Randomwaves/Synthgirl/02 Software/Synthgirl-App-H723/Data/Design 480x854/Image_Osc_B.bmp

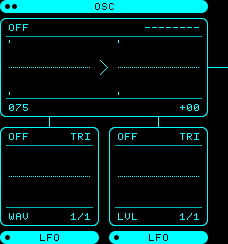
02 Software/Synthgirl-App-H723/Data/Design 480x854/Image_Osc_B.bmp
