Randomwaves/Synthgirl/02 Software/Synthgirl-App-H723/Data/Lfo/Lfo.pde

//int[] tri1  = {0, 128, 256, 384, 512, 640, 768, 896, 1024, 1152, 1280, 1408, 1536, 1664, 1792, 1920, 2048, 2176, 2304, 2432, 2560, 2688, 2816, 2944, 3072, 3200, 3328, 3456, 3584, 3712, 3840, 3968, 4096, 4224, 4352, 4480, 4608, 4736, 4864, 4992, 5120, 5248, 5376, 5504, 5632, 5760, 5888, 6016, 6144, 6272, 6400, 6528, 6656, 6784, 6912, 7040, 7168, 7296, 7424, 7552, 7680, 7808, 7936, 8064, 8192, 8320, 8448, 8576, 8704, 8832, 8960, 9088, 9216, 9344, 9472, 9600, 9728, 9856, 9984, 10112, 10240, 10368, 10496, 10624, 10752, 10880, 11008, 11136, 11264, 11392, 11520, 11648, 11776, 11904, 12032, 12160, 12288, 12416, 12544, 12672, 12800, 12928, 13056, 13184, 13312, 13440, 13568, 13696, 13824, 13952, 14080, 14208, 14336, 14464, 14592, 14720, 14848, 14976, 15104, 15232, 15360, 15488, 15616, 15744, 15872, 16000, 16128, 16256, 16384, 16512, 16640, 16768, 16896, 17024, 17152, 17280, 17408, 17536, 17664, 17792, 17920, 18048, 18176, 18304, 18432, 18560, 18688, 18816, 18944, 19072, 19200, 19328, 19456, 19584, 19712, 19840, 19968, 20096, 20224, 20352, 20480, 20608, 20736, 20864, 20992, 21120, 21248, 21376, 21504, 21632, 21760, 21888, 22016, 22144, 22272, 22400, 22528, 22656, 22784, 22912, 23040, 23168, 23296, 23424, 23552, 23680, 23808, 23936, 24064, 24192, 24320, 24448, 24576, 24704, 24832, 24960, 25088, 25216, 25344, 25472, 25600, 25728, 25856, 25984, 26112, 26240, 26368, 26496, 26624, 26752, 26880, 27008, 27136, 27264, 27392, 27520, 27648, 27776, 27904, 28032, 28160, 28288, 28416, 28544, 2867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
4, 46897, 47090, 47283, 47476, 47669, 47863, 48057, 48251, 48445, 48639, 48833, 49028, 49222, 49417, 49612, 49807, 50002, 50198, 50393, 50589, 50785, 50981, 51177, 51373, 51570, 51766, 51963, 52160, 52356, 52553, 52751, 52948, 53145, 53343, 53540, 53738, 53936, 54134, 54332, 54530, 54728, 54927, 55125, 55324, 55522, 55721, 55920, 56119, 56318, 56517, 56716, 56915, 57115, 57314, 57514, 57713, 57913, 58113, 58312, 58512, 58712, 58912, 59112, 59312, 59513, 59713, 59913, 60114, 60314, 60514, 60715, 60915, 61116, 61317, 61517, 61718, 61919, 62119, 62320, 62521, 62722, 62923, 63124, 63325, 63526, 63727, 63928, 64129, 64330, 64531, 64732, 64933, 65134, 65335, };

//int[] sine1 = {32768, 32969, 33170, 33371, 33572, 33773, 33974, 34175, 34376, 34577, 34777, 34978, 35179, 35379, 35579, 35780, 35980, 36180, 36380, 36580, 36779, 36979, 37178, 37377, 37576, 37775, 37973, 38172, 38370, 38568, 38766, 38963, 39161, 39358, 39555, 39751, 39948, 40144, 40339, 40535, 40730, 40925, 41119, 41314, 41508, 41701, 41895, 42087, 42280, 42472, 42664, 42856, 43047, 43237, 43428, 43618, 43807, 43996, 44185, 44373, 44561, 44748, 44935, 45122, 45308, 45493, 45678, 45863, 46047, 46231, 46414, 46596, 46778, 46960, 47141, 47321, 47501, 47680, 47859, 48037, 48215, 48392, 48568, 48744, 48919, 49094, 49268, 49441, 49614, 49786, 49958, 50129, 50299, 50468, 50637, 50805, 50973, 51140, 51306, 51471, 51636, 51800, 51963, 52126, 52288, 52449, 52609, 52769, 52928, 53086, 53243, 53400, 53556, 53711, 53865, 54019, 54171, 54323, 54474, 54624, 54774, 54922, 55070, 55217, 55363, 55508, 55652, 55796, 55938, 56080, 56221, 56361, 56500, 56638, 56776, 56912, 57047, 57182, 57316, 57448, 57580, 57711, 57841, 57970, 58098, 58225, 58351, 58476, 58601, 58724, 58846, 58967, 59088, 59207, 59325, 59442, 59559, 59674, 59788, 59901, 60014, 60125, 60235, 60344, 60452, 60559, 60665, 60770, 60874, 60977, 61079, 61179, 61279, 61378, 61475, 61571, 61667, 61761, 61854, 61946, 62037, 62127, 62216, 62303, 62390, 62475, 62560, 62643, 62725, 62806, 62886, 62964, 63042, 63118, 63193, 63267, 63340, 63412, 63483, 63552, 63621, 63688, 63754, 63818, 63882, 63945, 64006, 64066, 64125, 64183, 64239, 64295,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
1365, 11517, 11671, 11825, 11980, 12136, 12293, 12450, 12608, 12767, 12927, 13087, 13248, 13410, 13573, 13736, 13900, 14065, 14230, 14396, 14563, 14731, 14899, 15068, 15237, 15407, 15578, 15750, 15922, 16095, 16268, 16442, 16617, 16792, 16968, 17144, 17321, 17499, 17677, 17856, 18035, 18215, 18395, 18576, 18758, 18940, 19122, 19305, 19489, 19673, 19858, 20043, 20228, 20414, 20601, 20788, 20975, 21163, 21351, 21540, 21729, 21918, 22108, 22299, 22489, 22680, 22872, 23064, 23256, 23449, 23641, 23835, 24028, 24222, 24417, 24611, 24806, 25001, 25197, 25392, 25588, 25785, 25981, 26178, 26375, 26573, 26770, 26968, 27166, 27364, 27563, 27761, 27960, 28159, 28358, 28557, 28757, 28956, 29156, 29356, 29556, 29756, 29957, 30157, 30357, 30558, 30759, 30959, 31160, 31361, 31562, 31763, 31964, 32165, 32366, 32567};
//int[] sine2 = {32768, 33170, 33572, 33974, 34376, 34777, 35179, 35579, 35980, 36380, 36779, 37178, 37576, 37973, 38370, 38766, 39161, 39555, 39948, 40339, 40730, 41119, 41508, 41895, 42280, 42664, 43047, 43428, 43807, 44185, 44561, 44935, 45308, 45678, 46047, 46414, 46778, 47141, 47501, 47859, 48215, 48568, 48919, 49268, 49614, 49958, 50299, 50637, 50973, 51306, 51636, 51963, 52288, 52609, 52928, 53243, 53556, 53865, 54171, 54474, 54774, 55070, 55363, 55652, 55938, 56221, 56500, 56776, 57047, 57316, 57580, 57841, 58098, 58351, 58601, 58846, 59088, 59325, 59559, 59788, 60014, 60235, 60452, 60665, 60874, 61079, 61279, 61475, 61667, 61854, 62037, 62216, 62390, 62560, 62725, 62886, 63042, 63193, 63340, 63483, 63621, 63754, 63882, 64006, 64125, 64239, 64349, 64454, 64554, 64649, 64740, 64826, 64906, 64982, 65054, 65120, 65181, 65238, 65290, 65336, 65378, 65415, 65447, 65474, 65497, 65514, 65526, 65534, 65536, 65534, 65526, 65514, 65497, 65474, 65447, 65415, 65378, 65336, 65290, 65238, 65181, 65120, 65054, 64982, 64906, 64826, 64740, 64649, 64554, 64454, 64349, 64239, 64125, 64006, 63882, 63754, 63621, 63483, 63340, 63193, 63042, 62886, 62725, 62560, 62390, 62216, 62037, 61854, 61667, 61475, 61279, 61079, 60874, 60665, 60452, 60235, 60014, 59788, 59559, 59325, 59088, 58846, 58601, 58351, 58098, 57841, 57580, 57316, 57047, 56776, 56500, 56221, 55938, 55652, 55363, 55070, 54774, 54474, 54171, 53865, 53556, 53243, 52928, 52609, 52288, 51963, 51636, 51306, 50973, 50637, 50299, 49958,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
33572, 32768, 31964, 31160, 30357, 29556, 28757, 27960, 27166, 26375, 25588, 24806, 24028, 23256, 22489, 21729, 20975, 20228, 19489, 18758, 18035, 17321, 16617, 15922, 15237, 14563, 13900, 13248, 12608, 11980, 11365, 10762, 10173, 9598, 9036, 8489, 7956, 7438, 6935, 6448, 5977, 5522, 5084, 4662, 4257, 3869, 3499, 3146, 2811, 2494, 2196, 1915, 1654, 1411, 1187, 982, 796, 630, 482, 355, 246, 158, 89, 39, 10, 0, 10, 39, 89, 158, 246, 355, 482, 630, 796, 982, 1187, 1411, 1654, 1915, 2196, 2494, 2811, 3146, 3499, 3869, 4257, 4662, 5084, 5522, 5977, 6448, 6935, 7438, 7956, 8489, 9036, 9598, 10173, 10762, 11365, 11980, 12608, 13248, 13900, 14563, 15237, 15922, 16617, 17321, 18035, 18758, 19489, 20228, 20975, 21729, 22489, 23256, 24028, 24806, 25588, 26375, 27166, 27960, 28757, 29556, 30357, 31160, 31964};
//int[] sine3 = {32768, 33571, 34373, 35172, 35967, 36760, 37548, 38332, 39111, 39884, 40652, 41414, 42169, 42916, 43656, 44388, 45112, 45826, 46532, 47228, 47913, 48588, 49252, 49905, 50546, 51175, 51792, 52396, 52987, 53565, 54129, 54679, 55214, 55735, 56241, 56732, 57207, 57667, 58111, 58538, 58949, 59344, 59721, 60082, 60425, 60751, 61059, 61350, 61623, 61877, 62114, 62333, 62533, 62714, 62878, 63023, 63149, 63256, 63345, 63416, 63467, 63501, 63515, 63511, 63488, 63447, 63387, 63309, 63213, 63098, 62966, 62815, 62647, 62461, 62257, 62036, 61798, 61543, 61270, 60982, 60677, 60355, 60018, 59665, 59296, 58912, 58514, 58100, 57672, 57230, 56774, 56305, 55822, 55327, 54819, 54298, 53766, 53223, 52668, 52102, 51526, 50939, 50344, 49738, 49124, 48501, 47870, 47232, 46586, 45933, 45273, 44608, 43936, 43260, 42578, 41892, 41203, 40509, 39812, 39113, 38412, 37708, 37003, 36297, 35591, 34884, 34178, 33472, 32768, 32065, 31364, 30666, 29970, 29278, 28589, 27904, 27224, 26549, 25879, 25215, 24556, 23905, 23260, 22622, 21992, 21369, 20755, 20150, 19554, 18967, 18390, 17822, 17265, 16719, 16184, 15660, 15147, 14646, 14158, 13682, 13218, 12767, 12330, 11905, 11495, 11098, 10715, 10347, 9992, 9653, 9328, 9018, 8723, 8444, 8179, 7931, 7698, 7480, 7279, 7093, 6923, 6769, 6631, 6510, 6404, 6315, 6242, 6185, 6145, 6120, 6112, 6120, 6144, 6184, 6240, 6312, 6400, 6503, 6622, 6757, 6907, 7072, 7252, 7448, 7658, 7883, 8122, 8376, 8644, 8925, 9221, 9530, 9852, 10188, 10536, 10896, 11270, 11655, 12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
 32768, 32768, 32768, 32768, 32768, 32768, 32768, 32768, 32768, 32768, 32768, 32768, 32768, 32768, 32768, 32768, 32768, 32768, 32768, 32768, 32768, 32768, 32768, 8192, 8192, 8192, 8192, 8192, 8192, 8192, 8192, 8192, 8192, 8192, 8192, 8192, 8192, 8192, 8192, 8192, 8192, 8192, 8192, 8192, 8192, 8192, 8192, 8192, 8192, 8192, 8192, 8192, 8192, 8192, 8192, 8192, 8192, 8192, 8192, 8192, 8192, 8192, 8192, 8192, 8192, 8192, 8192, 8192, 8192, 8192, 8192, 8192, 8192, 8192, 8192, 8192, 8192, 8192, 8192, 8192, 8192, 8192, 8192, 8192, 8192, 8192, 8192, 8192, 8192, 8192, 8192, 8192, 8192, 8192, 8192, 8192, 8192, 8192, 8192, 8192, 8192, 8192, 8192, 8192, 8192, 8192, 8192, 8192, 8192, 8192, 8192, 8192, 8192, 8192, 8192, 8192, 8192, 8192, 8192, 8192, 8192, 8192, 8192, 8192, 8192, 8192, 8192, 8192, 8192, 8192, 8192, 8192, 8192, 8192, 8192, 8192, 8192, 8192, 8192, 8192, 8192, 8192, 8192, 8192, 8192, 8192, 8192, 8192, 8192, 8192, 8192};

int[] shot1 = {0, 1608, 3216, 4821, 6424, 8022, 9616, 11204, 12785, 14359, 15924, 17479, 19024, 20557, 22078, 23586, 25080, 26558, 28020, 29466, 30893, 32303, 33692, 35062, 36410, 37736, 39040, 40320, 41576, 42806, 44011, 45190, 46341, 47464, 48559, 49624, 50660, 51665, 52639, 53581, 54491, 55368, 56212, 57022, 57798, 58538, 59244, 59914, 60547, 61145, 61705, 62228, 62714, 63162, 63572, 63944, 64277, 64571, 64827, 65043, 65220, 65358, 65457, 65516, 65536, 65516, 65457, 65358, 65220, 65043, 64827, 64571, 64277, 63944, 63572, 63162, 62714, 62228, 61705, 61145, 60547, 59914, 59244, 58538, 57798, 57022, 56212, 55368, 54491, 53581, 52639, 51665, 50660, 49624, 48559, 47464, 46341, 45190, 44011, 42806, 41576, 40320, 39040, 37736, 36410, 35062, 33692, 32303, 30893, 29466, 28020, 26558, 25080, 23586, 22078, 20557, 19024, 17479, 15924, 14359, 12785, 11204, 9616, 8022, 6424, 4821, 3216, 1608, 0, 0, 0, 1, 2, 3, 4, 5, 7, 8, 10, 12, 15, 17, 20, 23, 26, 30, 33, 37, 41, 45, 50, 54, 59, 64, 69, 75, 81, 86, 92, 99, 105, 112, 119, 126, 133, 141, 148, 156, 164, 173, 181, 190, 199, 208, 217, 227, 237, 247, 257, 267, 278, 289, 299, 311, 322, 334, 345, 357, 370, 382, 395, 407, 421, 434, 447, 461, 475, 489, 503, 517, 532, 547, 562, 577, 593, 608, 624, 640, 657, 673, 690, 707, 724, 741, 758, 776, 794, 812, 830, 849, 868, 887, 906, 925, 944, 964, 984, 1004, 1025, 1045, 1066, 1087, 1108, 1129, 1151, 1172, 1194, 1216, 1239, 1261, 1284, 1307, 1330, 1353, 1377, 1401, 1425, 1449, 1473, 1498, 1522, 1547, 15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
 46478, 46279, 46072, 45858, 45638, 45411, 45176, 44935, 44687, 44433, 44172, 43904, 43629, 43348, 43061, 42767, 42466, 42159, 41846, 41526, 41200, 40868, 40530, 40186, 39836, 39479, 39117, 38749, 38375, 37995, 37610, 37218, 36822, 36419, 36011, 35598, 35180, 34756, 34327, 33892, 33453, 33008, 32559, 32105, 31646, 31182, 30713, 30240, 29762, 29280, 28793, 28302, 27807, 27307, 26804, 26296, 25785, 25269, 24750, 24227, 23700, 23170, 22636, 22099, 21559, 21015, 20468, 19918, 19365, 18810, 18251, 17690, 17125, 16559, 15990, 15418, 14844, 14268, 13690, 13109, 12527, 11943, 11357, 10769, 10180, 9589, 8997, 8403, 7808, 7212, 6615, 6017, 5418, 4818, 4217, 3616, 3014, 2412, 1809, 1206, 603};
int[] shot2 = {0, 3216, 6424, 9616, 12785, 15924, 19024, 22078, 25080, 28020, 30893, 33692, 36410, 39040, 41576, 44011, 46341, 48559, 50660, 52639, 54491, 56212, 57798, 59244, 60547, 61705, 62714, 63572, 64277, 64827, 65220, 65457, 65536, 65457, 65220, 64827, 64277, 63572, 62714, 61705, 60547, 59244, 57798, 56212, 54491, 52639, 50660, 48559, 46341, 44011, 41576, 39040, 36410, 33692, 30893, 28020, 25080, 22078, 19024, 15924, 12785, 9616, 6424, 3216, 0, 1287, 2573, 3857, 5139, 6418, 7693, 8963, 10228, 11487, 12739, 13983, 15219, 16446, 17663, 18869, 20064, 21246, 22416, 23573, 24715, 25842, 26954, 28049, 29128, 30189, 31232, 32256, 33260, 34245, 35209, 36152, 37073, 37971, 38847, 39700, 40528, 41332, 42111, 42865, 43593, 44295, 44970, 45618, 46238, 46831, 47395, 47931, 48438, 48916, 49364, 49783, 50171, 50530, 50858, 51155, 51421, 51657, 51861, 52035, 52176, 52287, 52366, 52413, 52429, 52413, 52366, 52287, 52176, 52035, 51861, 51657, 51421, 51155, 50858, 50530, 50171, 49783, 49364, 48916, 48438, 47931, 47395, 46831, 46238, 45618, 44970, 44295, 43593, 42865, 42111, 41332, 40528, 39700, 38847, 37971, 37073, 36152, 35209, 34245, 33260, 32256, 31232, 30189, 29128, 28049, 26954, 25842, 24715, 23573, 22416, 21246, 20064, 18869, 17663, 16446, 15219, 13983, 12739, 11487, 10228, 8963, 7693, 6418, 5139, 3857, 2573, 1287, 0, 483, 965, 1447, 1929, 2411, 2893, 3374, 3854, 4334, 4813, 5292, 5770, 6247, 6722, 7197, 7671, 8144, 8615, 9086, 9554, 10022, 10488, 10952, 11414, 11875, 12334, 12792,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
37, 18737, 18637, 18536, 18435, 18333, 18231, 18128, 18024, 17920, 17815, 17710, 17605, 17498, 17392, 17284, 17177, 17068, 16960, 16850, 16741, 16630, 16519, 16408, 16296, 16184, 16072, 15958, 15845, 15731, 15616, 15501, 15385, 15269, 15153, 15036, 14919, 14801, 14683, 14564, 14445, 14325, 14205, 14085, 13964, 13843, 13721, 13599, 13477, 13354, 13231, 13107, 12983, 12859, 12734, 12609, 12483, 12357, 12231, 12104, 11977, 11850, 11722, 11594, 11466, 11337, 11208, 11079, 10949, 10819, 10688, 10558, 10427, 10295, 10164, 10032, 9900, 9767, 9634, 9501, 9368, 9234, 9100, 8966, 8831, 8697, 8562, 8426, 8291, 8155, 8019, 7883, 7746, 7610, 7473, 7336, 7198, 7061, 6923, 6785, 6647, 6508, 6370, 6231, 6092, 5953, 5813, 5674, 5534, 5394, 5254, 5114, 4974, 4833, 4693, 4552, 4411, 4270, 4129, 3988, 3846, 3705, 3563, 3422, 3280, 3138, 2996, 2854, 2712, 2569, 2427, 2285, 2142, 2000, 1857, 1715, 1572, 1429, 1286, 1143, 1001, 858, 715, 572, 429, 286, 143};
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
